rosscon/Rook/Mods/Hotend/MGN9C_HotendMount.stl

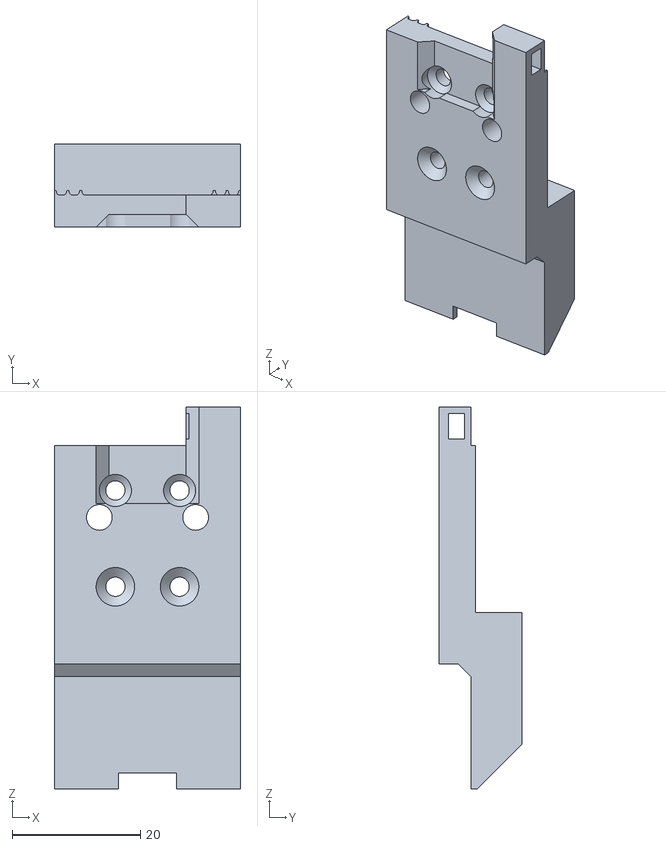
[picture p22: CAD file, 2023-01-01]
Mods/Hotend/MGN9C_HotendMount.stl
29.0 x 13.0 x 59.5
