rosscon/Rook/Mods/PrintBed/PrintBedFrame.stl

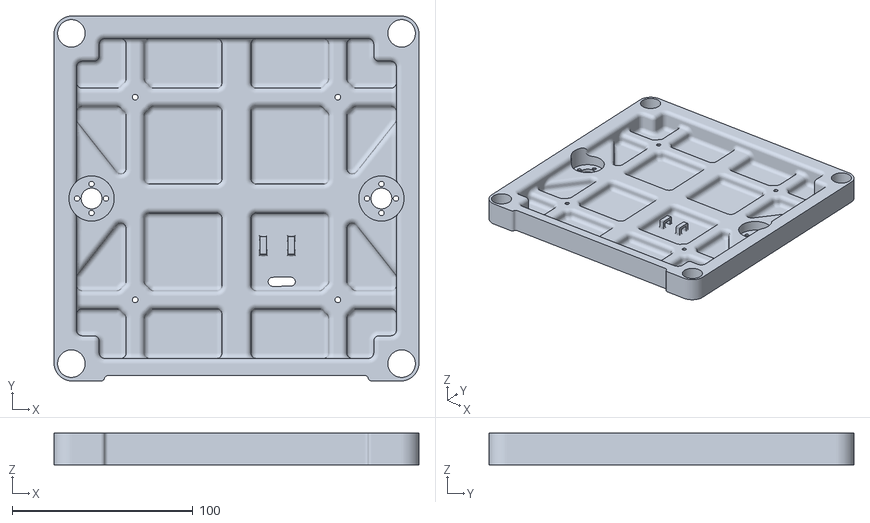
[picture p23: CAD file, 2022-11-28]
Mods/PrintBed/PrintBedFrame.stl
201.7 x 201.7 x 17.5
