rosscon/Rook/STLs/Layer Cooling/120mm blower_Mount.stl

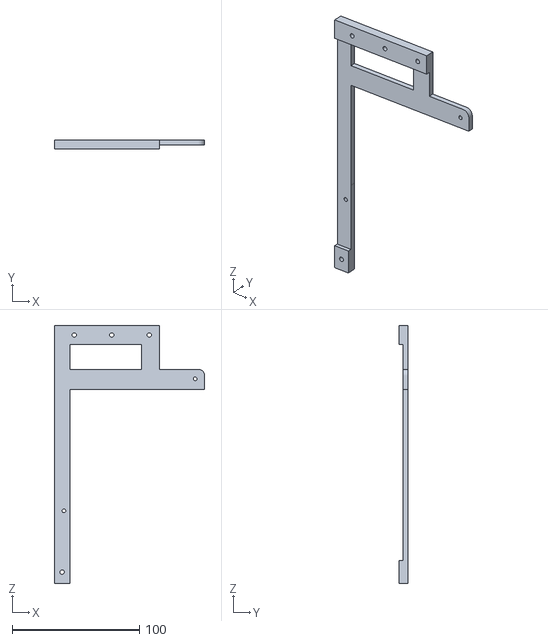
[picture p24: CAD file, 2022-12-05]
STLs/Layer Cooling/120mm blower_Mount.stl
118.4 x 7.00 x 203.0
