rosscon/Rook/STLs/X_Carriage_CR10_Style.stl

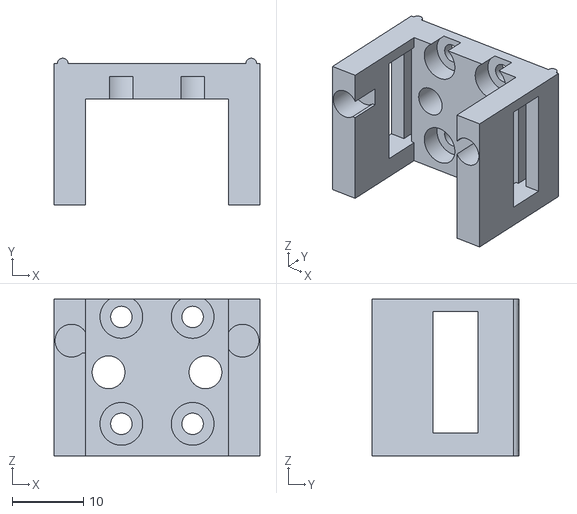
[picture p25: CAD file, 2022-12-05]
STLs/X_Carriage_CR10_Style.stl
28.9 x 20.6 x 22.0
