rosscon/Rook/User_Mods/Mods by Gulsifer/Rook_Rod_All_linear_Rod_version/CAD/V1Rook_Top Frame ROD MOD.STEP

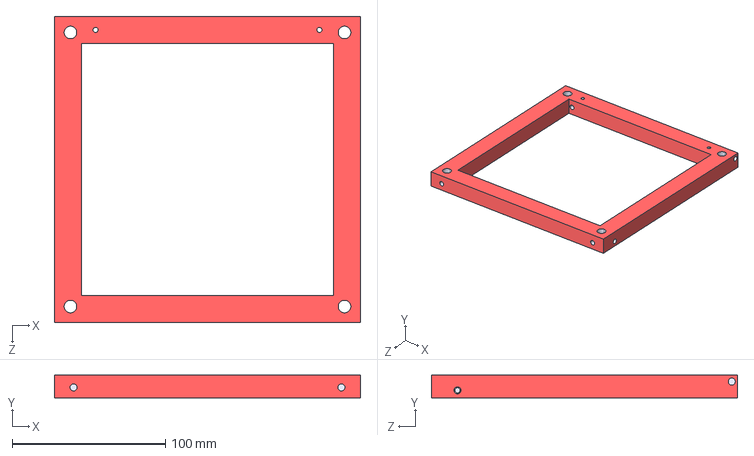
[picture p26: CAD file, 2022-12-05]
User_Mods/Mods by Gulsifer/Rook_Rod_All_linear_Rod_version/CAD/V1Rook_Top Frame ROD MOD.STEP
200.0 x 15.0 x 200.0 mm
