rosscon/Rook/User_Mods/Mods by Leviathan3DPrinting/Ender 3 v2 motor mounts/STLs/Y_MOTOR.stl

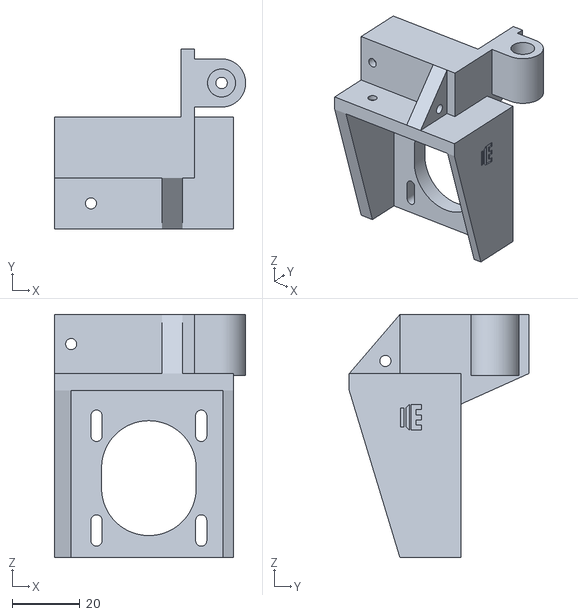
[picture p27: CAD file, 2022-12-05]
User_Mods/Mods by Leviathan3DPrinting/Ender 3 v2 motor mounts/STLs/Y_MOTOR.stl
56.7 x 53.2 x 71.9
