rosscon/Rook/Mods/Fan Bracket/FanBracket.stl

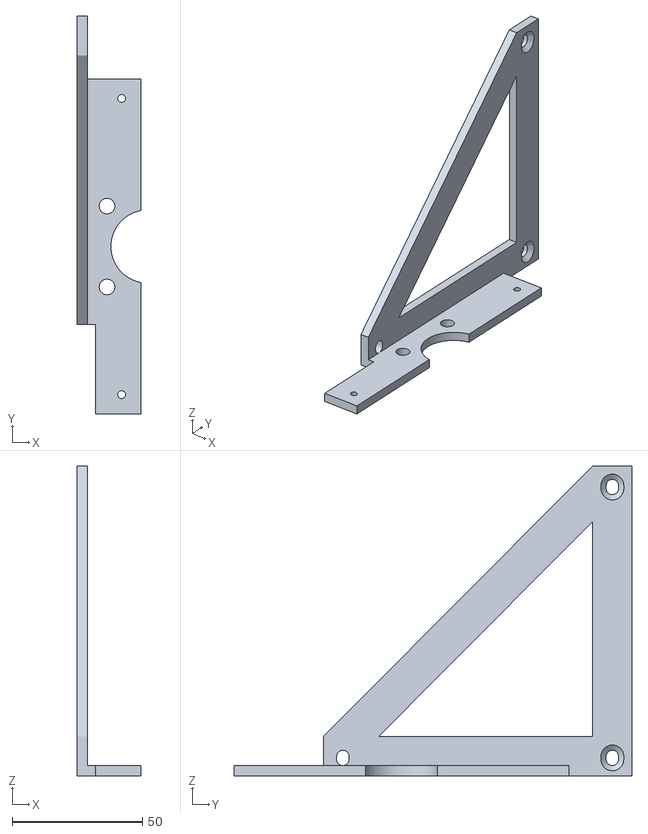
[picture p28: CAD file, 2022-11-20]
Mods/Fan Bracket/FanBracket.stl
24.5 x 152.5 x 118.8
