rosscon/Rook/Mods/Frame/exo_backbox.stl

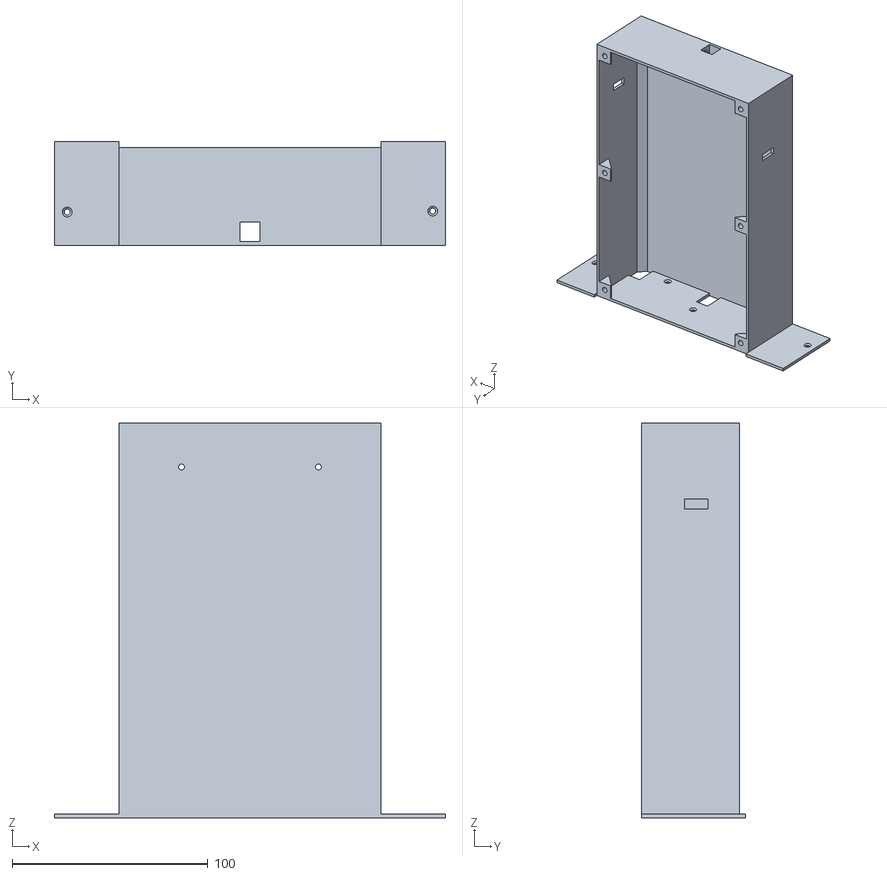
[picture p29: CAD file, 2023-01-01]
Mods/Frame/exo_backbox.stl
200.0 x 53.0 x 202.0
