rosscon/Rook/Mods/PrintBed/PrintBedTop.stl

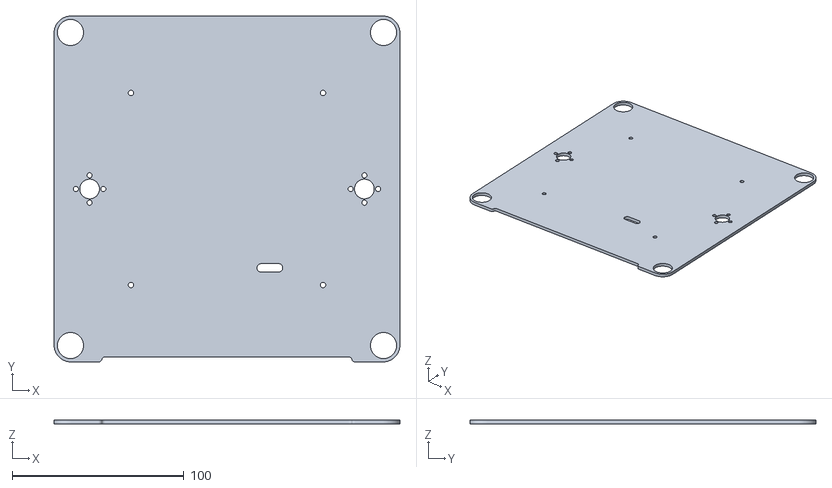
[picture p30: CAD file, 2022-11-28]
Mods/PrintBed/PrintBedTop.stl
201.7 x 201.7 x 2.50
