rosscon/Rook/STLs/Bed_Pad_for_springs.stl

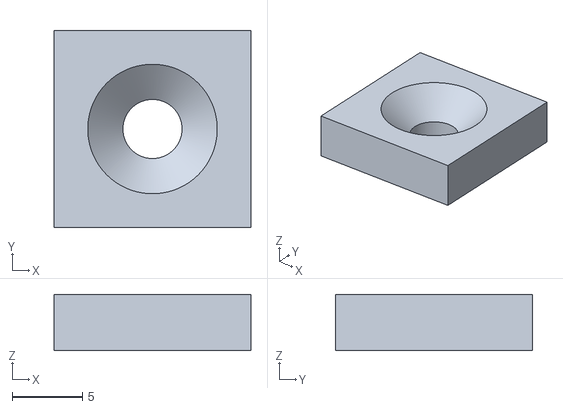
[picture p31: CAD file, 2022-12-05]
STLs/Bed_Pad_for_springs.stl
14.0 x 14.0 x 4.00
