rosscon/Rook/STLs/Frame/Top_Frame.stl

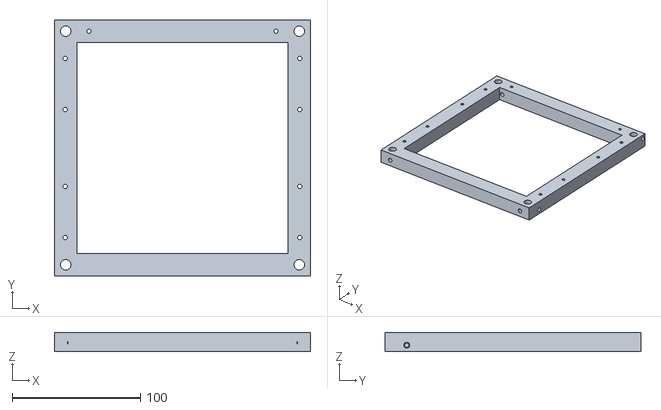
[picture p32: CAD file, 2022-12-05]
STLs/Frame/Top_Frame.stl
200.0 x 200.0 x 15.0
