rosscon/Rook/STLs/Gantry/Y_Carriage_Left_polished_MK1.stl

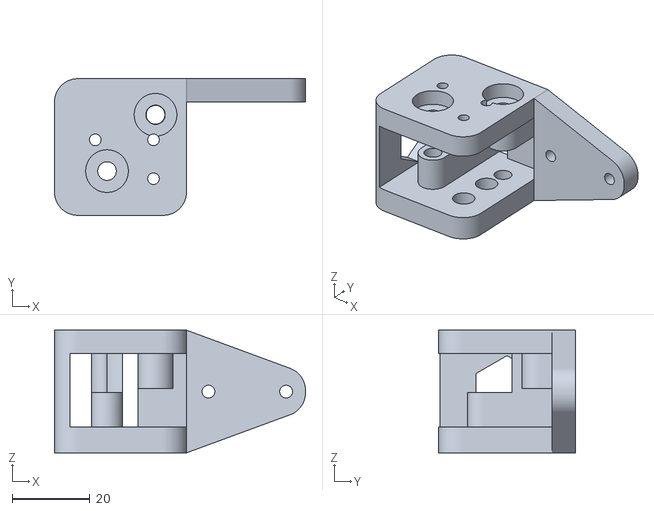
[picture p33: CAD file, 2022-12-05]
STLs/Gantry/Y_Carriage_Left_polished_MK1.stl
64.7 x 35.2 x 31.6
