rosscon/Rook/User_Mods/Mods by Gulsifer/Rook_Rod_All_linear_Rod_version/CAD/V1Y_Carriage_Right ROD MOD.STEP

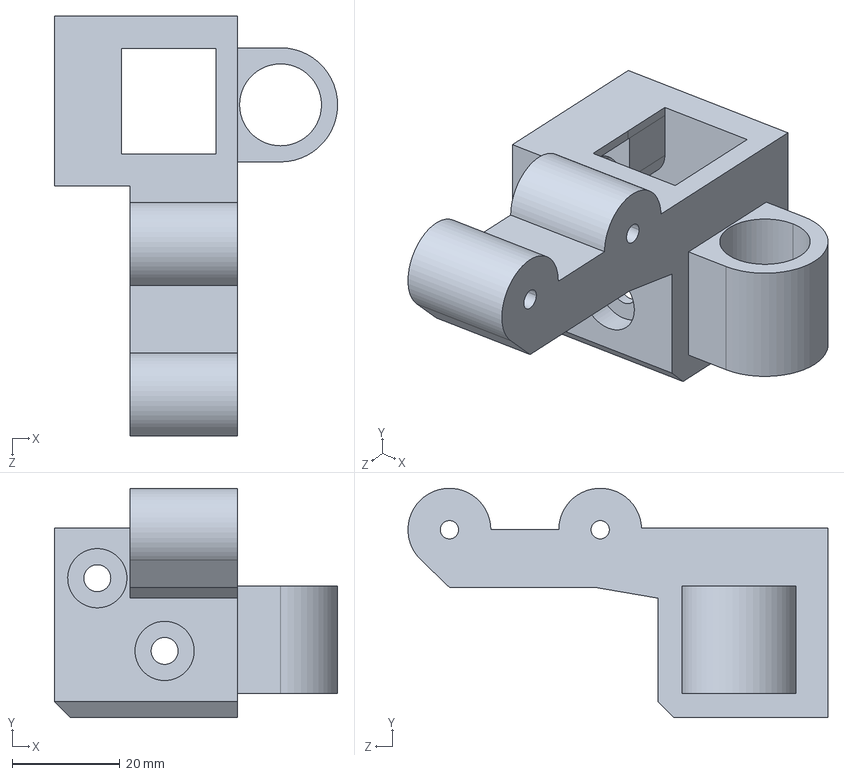
[picture p34: CAD file, 2022-12-05]
User_Mods/Mods by Gulsifer/Rook_Rod_All_linear_Rod_version/CAD/V1Y_Carriage_Right ROD MOD.STEP
52.6 x 42.6 x 78.0 mm
