rosscon/Rook/Mods/Frame/Endstop mount.stl

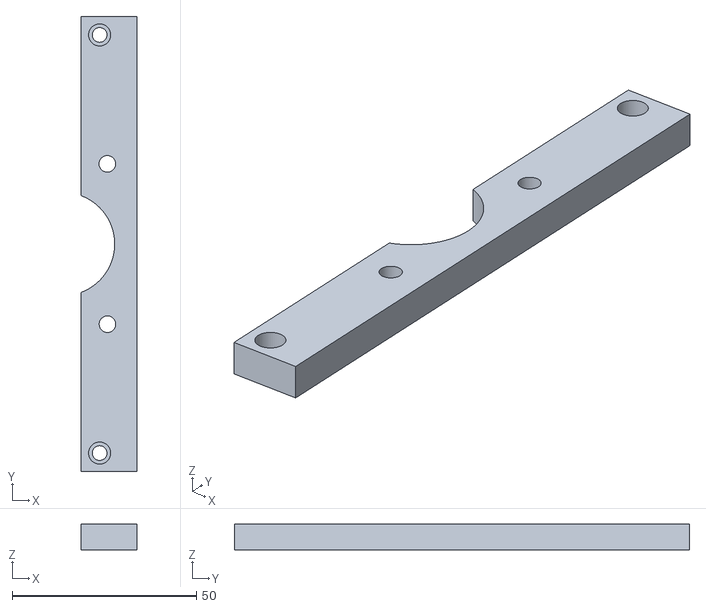
[picture p35: CAD file, 2023-01-01]
Mods/Frame/Endstop mount.stl
15.1 x 123.5 x 7.00
