rosscon/Rook/STLs/Frame/Bed_Frame.stl

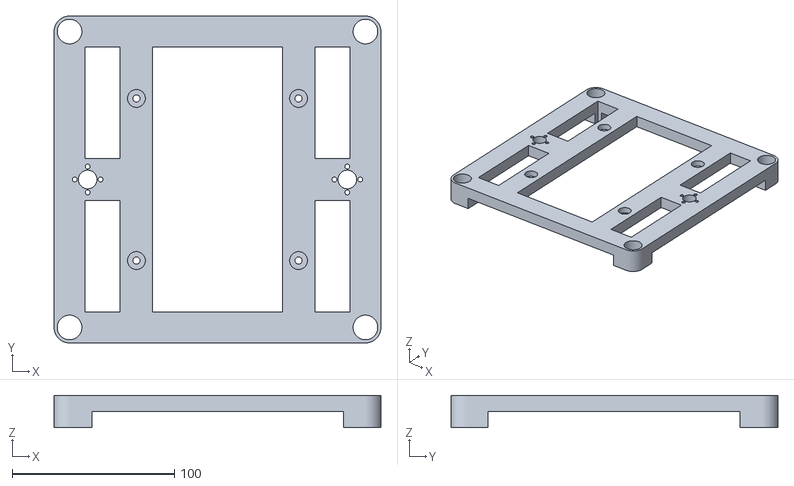
[picture p36: CAD file, 2022-12-05]
STLs/Frame/Bed_Frame.stl
201.7 x 201.7 x 20.0
