rosscon/Rook/User_Mods/Mods by Gulsifer/Rook_Rod_All_linear_Rod_version/CAD/V1Rook_Base Frame 2.1.STEP

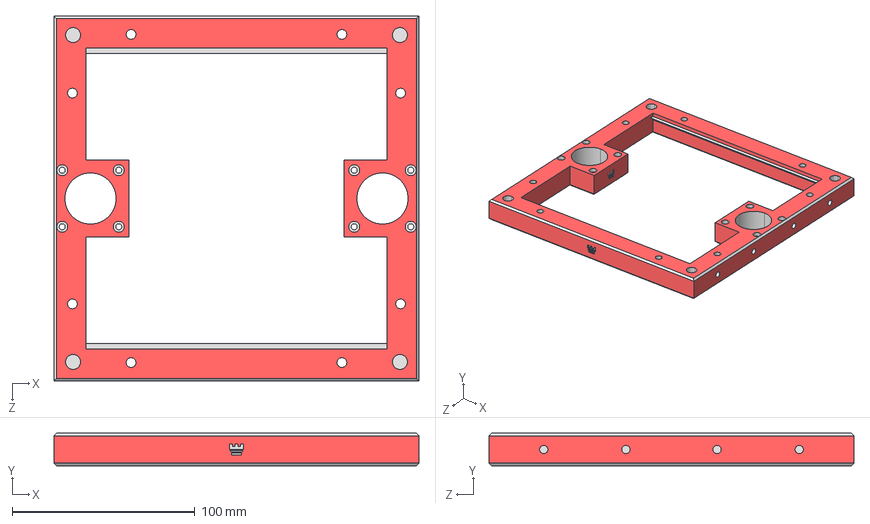
[picture p37: CAD file, 2022-12-05]
User_Mods/Mods by Gulsifer/Rook_Rod_All_linear_Rod_version/CAD/V1Rook_Base Frame 2.1.STEP
200.0 x 18.0 x 200.0 mm
