rosscon/Rook/Mods/Frame/Right_Motor_Mount.stl

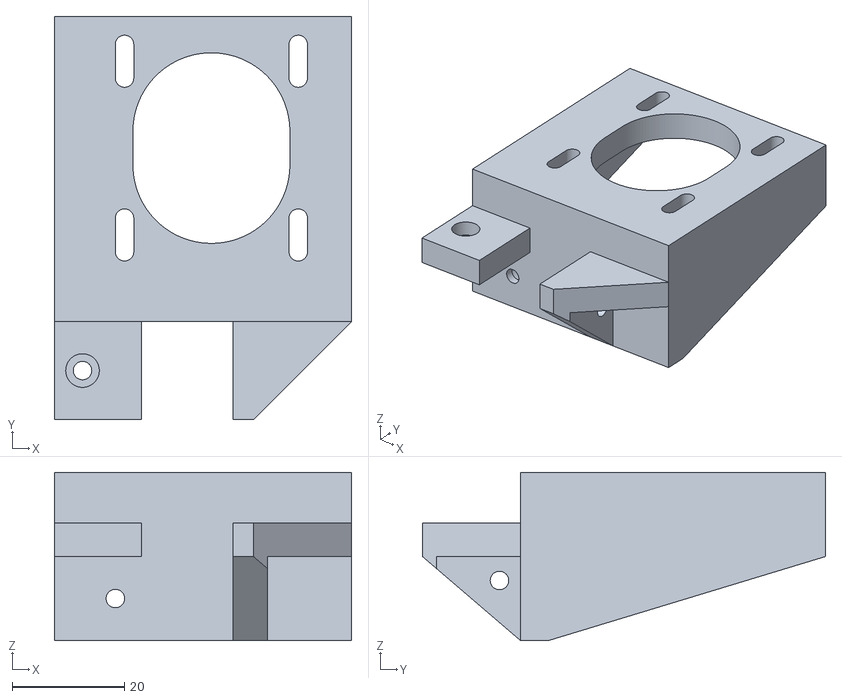
[picture p38: CAD file, 2023-01-01]
Mods/Frame/Right_Motor_Mount.stl
53.0 x 71.9 x 30.0
