rosscon/Rook/STLs/Frame/Z_endstop_Mount.stl

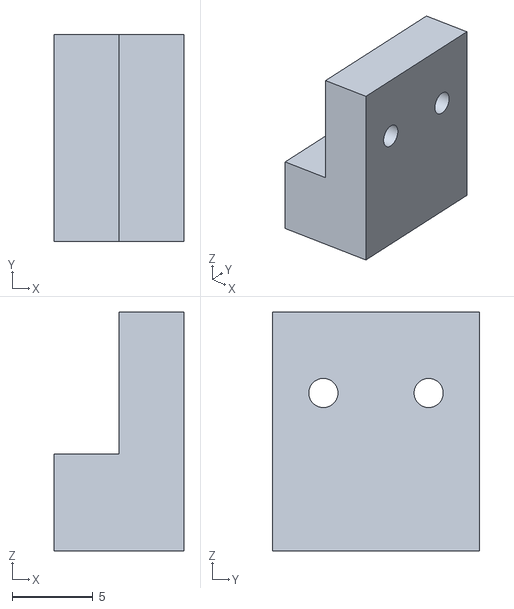
[picture p39: CAD file, 2022-12-05]
STLs/Frame/Z_endstop_Mount.stl
8.00 x 12.8 x 14.8
