rosscon/Rook/Mods/Frame/exo_backboxlid.stl

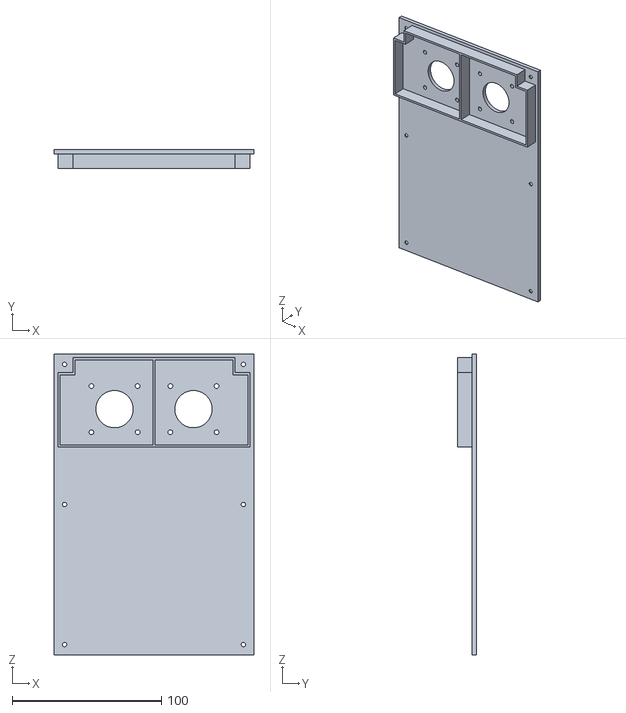
[picture p40: CAD file, 2023-01-01]
Mods/Frame/exo_backboxlid.stl
134.0 x 13.0 x 202.0
