rosscon/Rook/User_Mods/Mods by Gulsifer/Rook_Rod_All_linear_Rod_version/CAD/V1Right_Idler ROD MOD.STEP

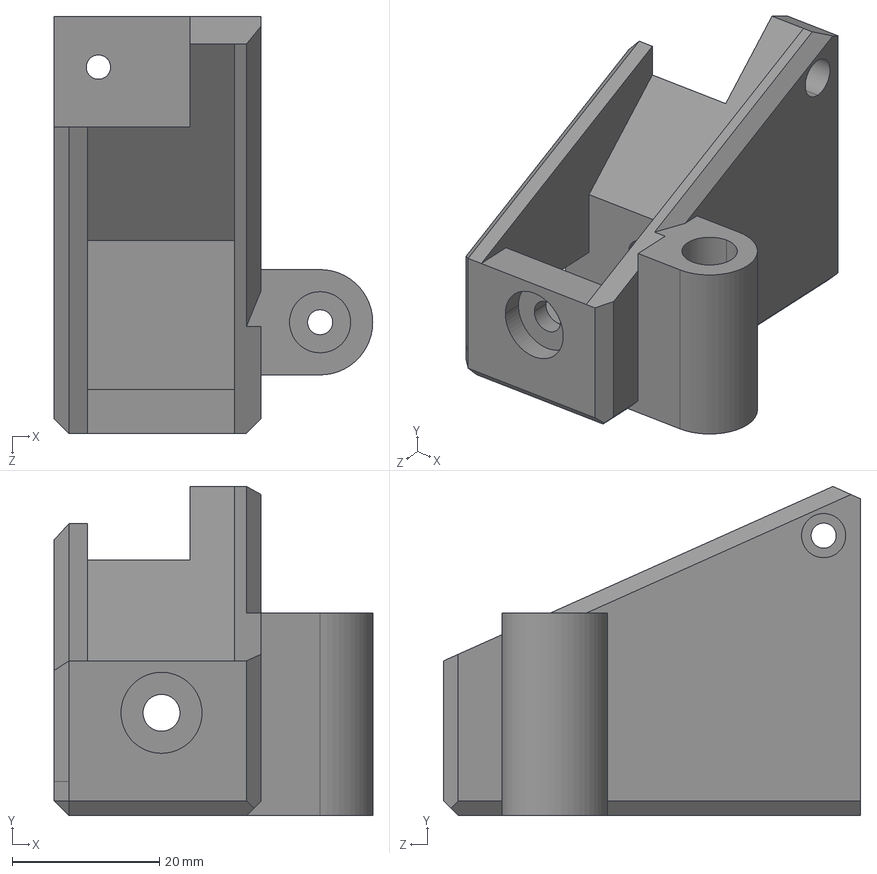
[picture p41: CAD file, 2022-12-05]
User_Mods/Mods by Gulsifer/Rook_Rod_All_linear_Rod_version/CAD/V1Right_Idler ROD MOD.STEP
43.2 x 44.7 x 56.6 mm
