rosscon/Rook/Mods/Frame/backbase.stl

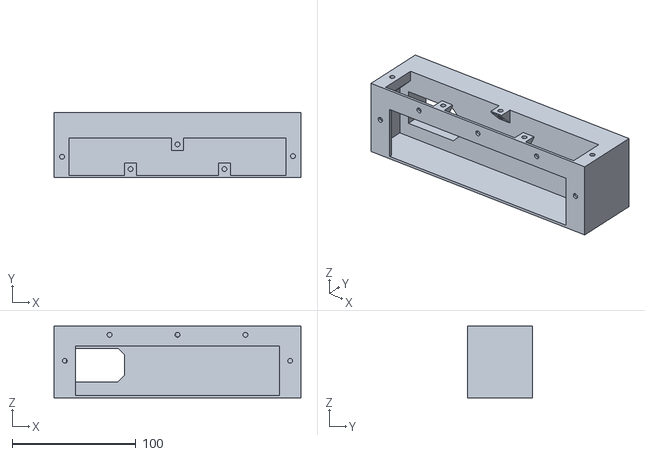
[picture p42: CAD file, 2023-01-01]
Mods/Frame/backbase.stl
200.0 x 53.0 x 58.0
