rosscon/Rook/User_Mods/Mods by Gulsifer/Rook_Rod_All_linear_Rod_version/CAD/V1Rook_Top Left Motor Mount ROD MOD.STEP

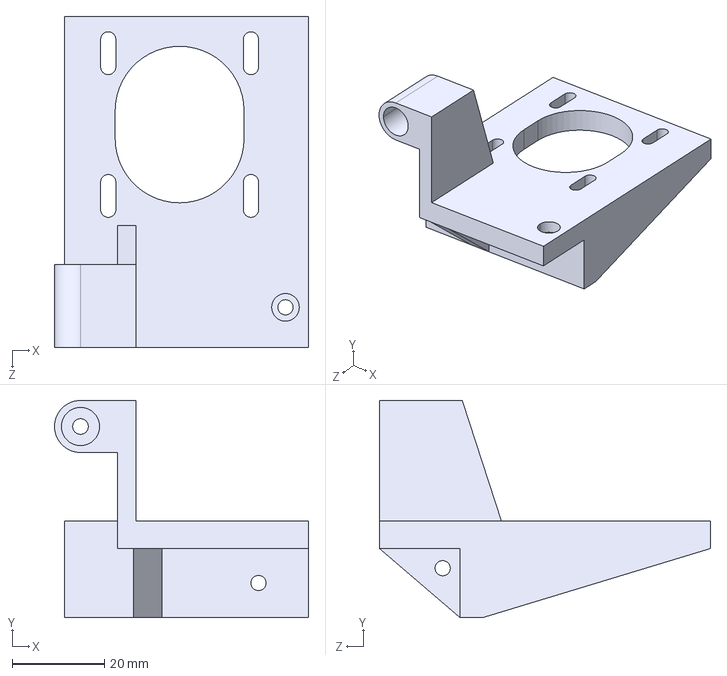
[picture p43: CAD file, 2022-12-05]
User_Mods/Mods by Gulsifer/Rook_Rod_All_linear_Rod_version/CAD/V1Rook_Top Left Motor Mount ROD MOD.STEP
55.2 x 47.2 x 72.0 mm
