rosscon/Rook/Mods/Frame/backbox_fan.stl

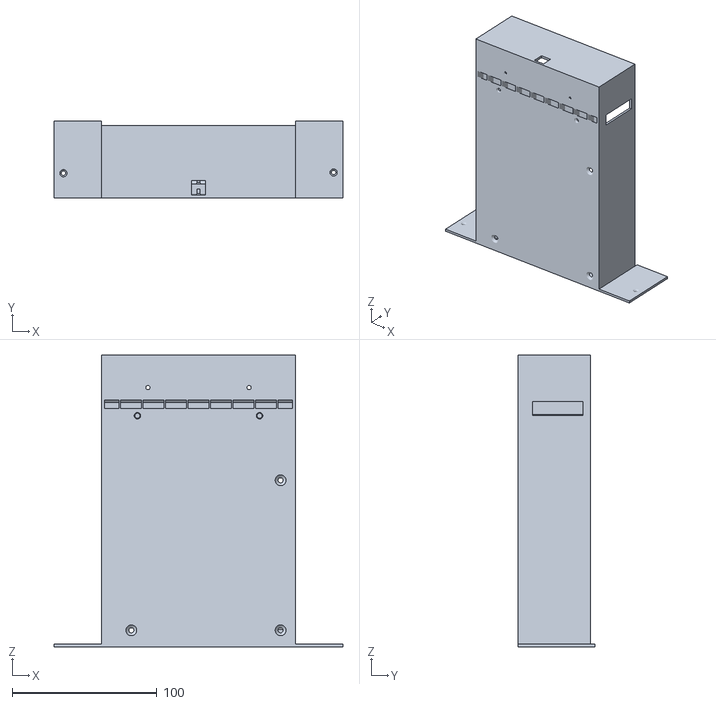
[picture p44: CAD file, 2023-01-01]
Mods/Frame/backbox_fan.stl
200.0 x 53.0 x 202.0
