rosscon/Rook/STLs/Frame/Left_Motor_Mount.stl

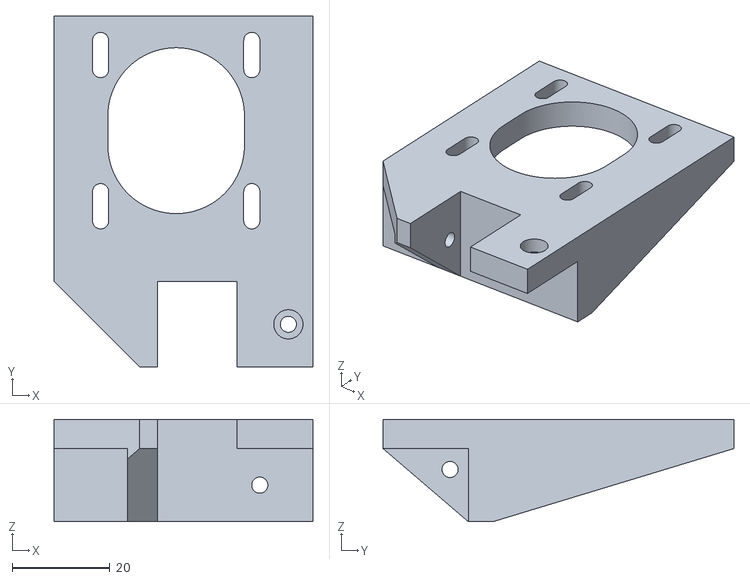
[picture p45: CAD file, 2022-12-05]
STLs/Frame/Left_Motor_Mount.stl
53.0 x 71.9 x 21.0
