rosscon/Rook/Mods/Frame/Bottom_Frame.stl

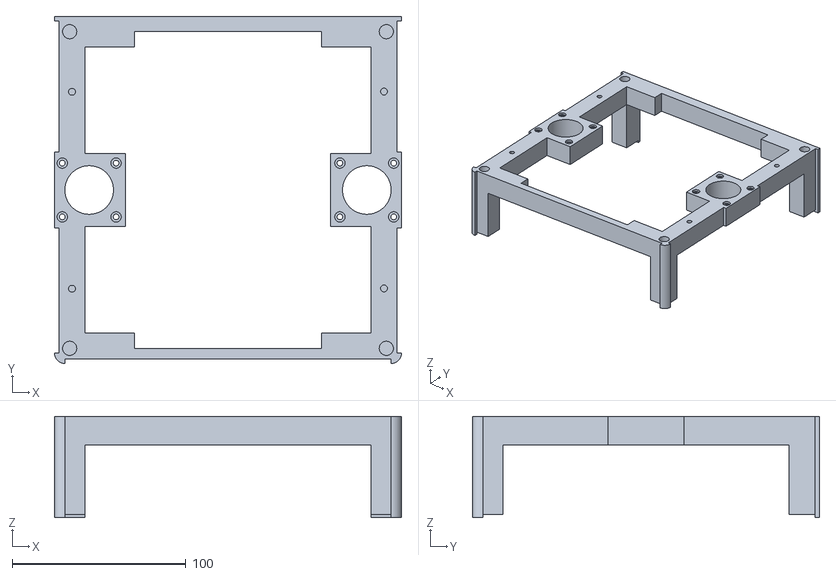
[picture p46: CAD file, 2022-12-12]
Mods/Frame/Bottom_Frame.stl
200.0 x 200.0 x 58.5
