rosscon/Rook/STLs/Frame/Bottom_Frame_MK1.stl

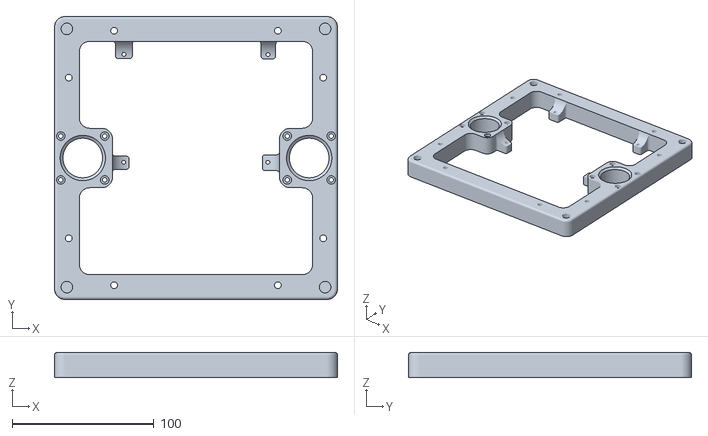
[picture p47: CAD file, 2022-12-05]
STLs/Frame/Bottom_Frame_MK1.stl
200.0 x 200.0 x 18.0
