rosscon/Rook/User_Mods/Mods by Gulsifer/Rook_Rod_All_linear_Rod_version/CAD/V1Left_Idler ROD MOD.STEP

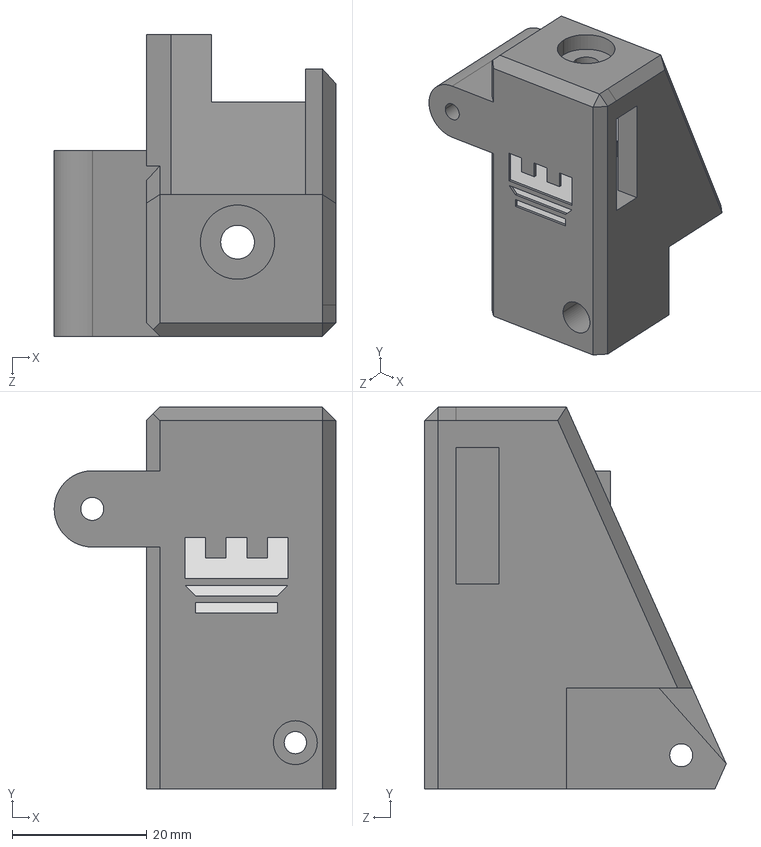
[picture p48: CAD file, 2022-12-05]
User_Mods/Mods by Gulsifer/Rook_Rod_All_linear_Rod_version/CAD/V1Left_Idler ROD MOD.STEP
41.7 x 56.6 x 44.7 mm
