rosscon/Rook/Mods/Frame/PSU_Safety Cover.stl

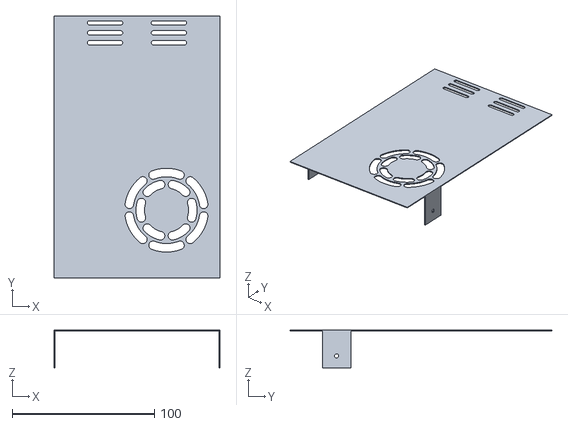
[picture p49: CAD file, 2022-12-12]
Mods/Frame/PSU_Safety Cover.stl
116.9 x 184.5 x 26.6
