rosscon/Rook/STLs/Frame/Right_Motor_Mount.stl

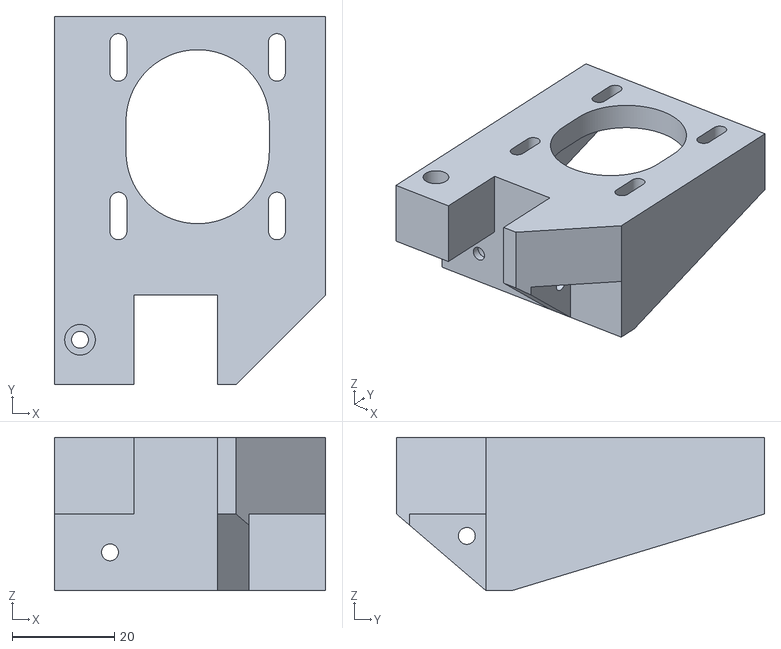
[picture p50: CAD file, 2022-12-05]
STLs/Frame/Right_Motor_Mount.stl
53.0 x 71.9 x 30.0
