rosscon/Rook/User_Mods/Mods by Gulsifer/Rook_Rod_All_linear_Rod_version/CAD/V1Rook_Top Right Motor Mount ROD MOD.STEP

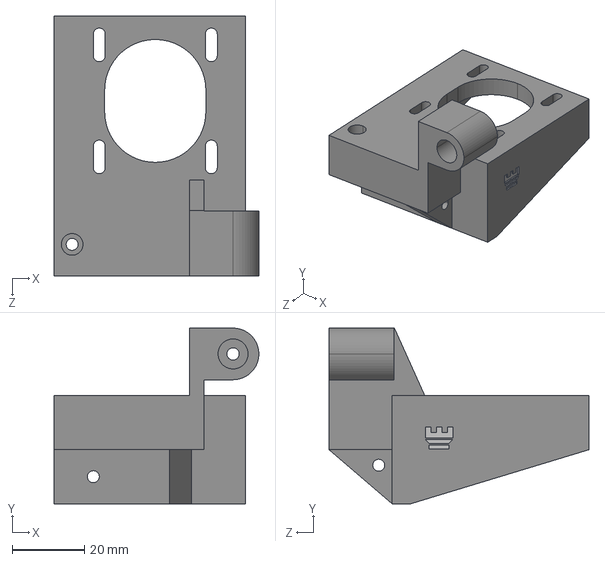
[picture p51: CAD file, 2022-12-05]
User_Mods/Mods by Gulsifer/Rook_Rod_All_linear_Rod_version/CAD/V1Rook_Top Right Motor Mount ROD MOD.STEP
56.7 x 48.6 x 72.0 mm
