rosscon/Rook/Mods/Frame/Bottom_Frame_topper.stl

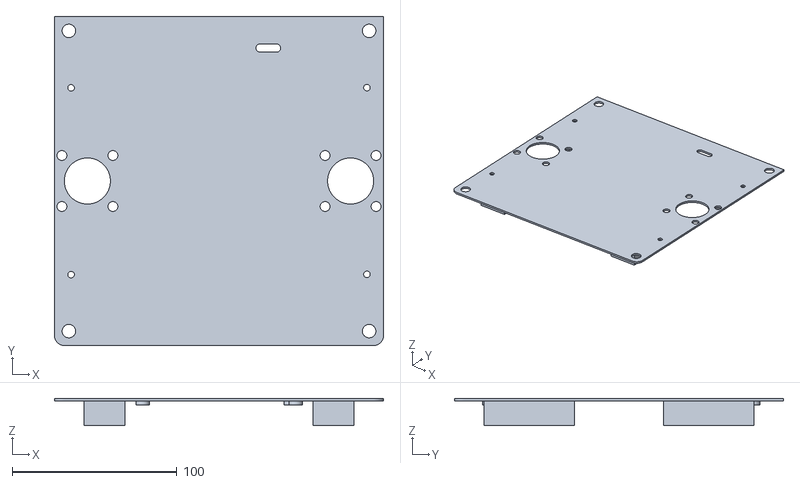
[picture p52: CAD file, 2022-12-12]
Mods/Frame/Bottom_Frame_topper.stl
200.0 x 200.0 x 16.5
