rosscon/Rook/User_Mods/Mods by Gulsifer/Rook_Rod_All_linear_Rod_version/CAD/V1Rook_Foot Mount_3.0.STEP

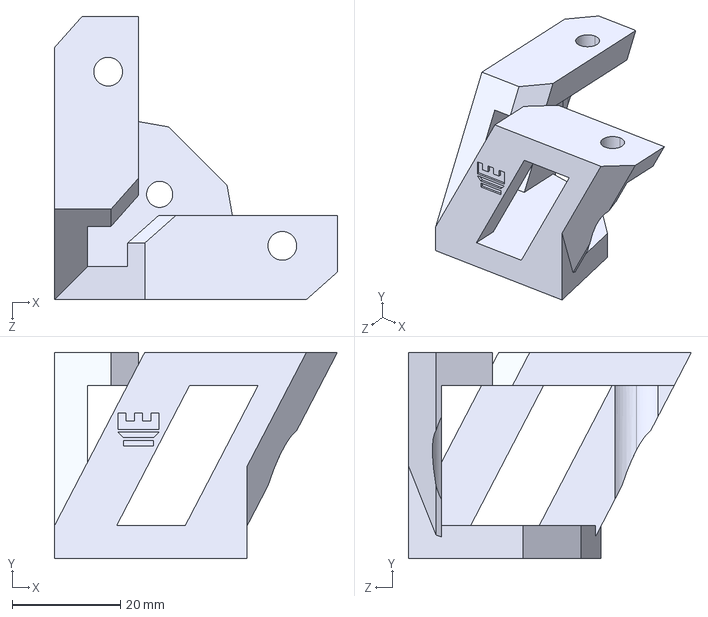
[picture p53: CAD file, 2022-12-05]
User_Mods/Mods by Gulsifer/Rook_Rod_All_linear_Rod_version/CAD/V1Rook_Foot Mount_3.0.STEP
52.2 x 38.1 x 52.2 mm
