rosscon/Rook/Mods/Frame/Fan Grill 40mm.stl

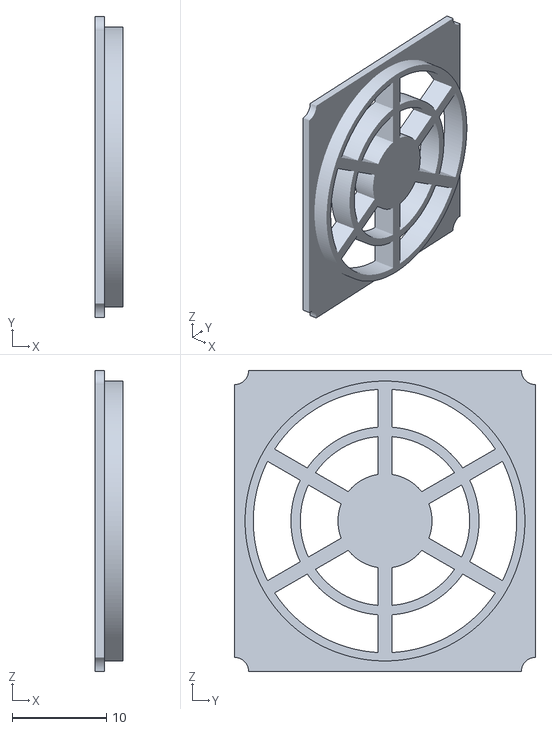
[picture p54: CAD file, 2022-12-05]
Mods/Frame/Fan Grill 40mm.stl
3.00 x 32.0 x 32.0
