rosscon/Rook/Mods/Frame/vent.stl

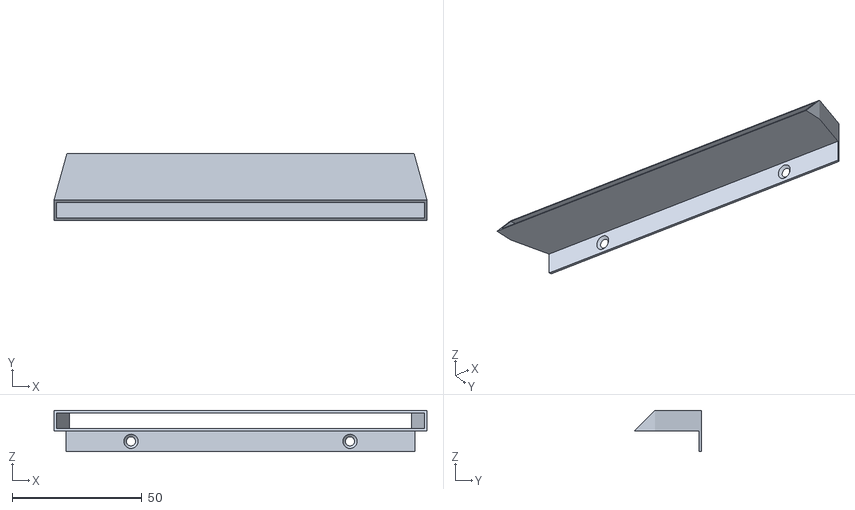
[picture p55: CAD file, 2022-12-05]
Mods/Frame/vent.stl
144.0 x 26.0 x 16.0
