rosscon/Rook/Mods/Frame/Bottom_Frame_pnl_fan_fl.stl

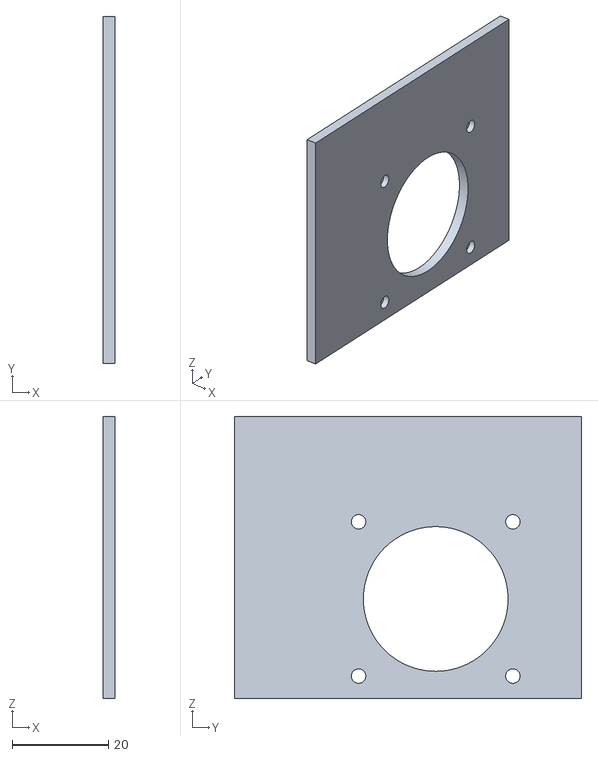
[picture p56: CAD file, 2022-11-28]
Mods/Frame/Bottom_Frame_pnl_fan_fl.stl
2.50 x 72.0 x 58.5
