rosscon/Rook/Mods/Frame/Bottom_Frame_pnl_fan_rr.stl

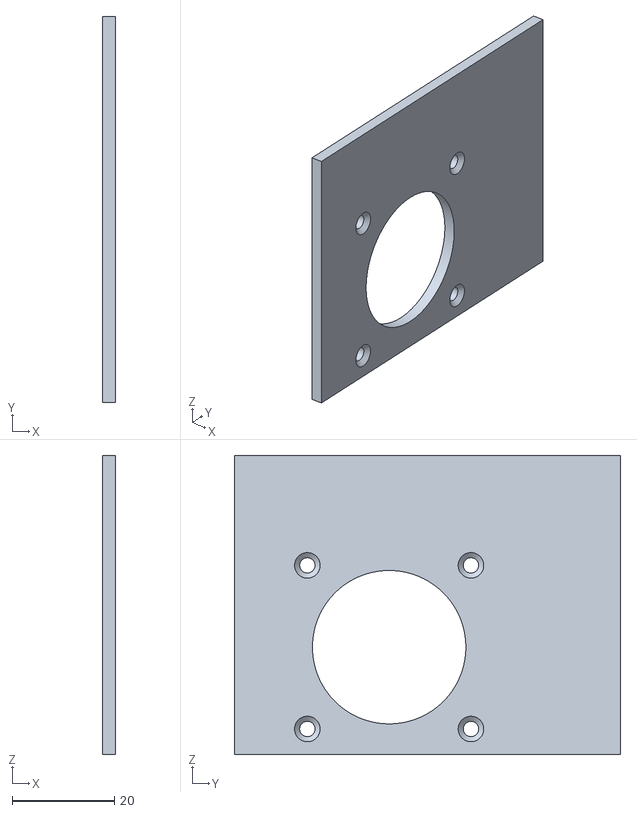
[picture p57: CAD file, 2022-11-28]
Mods/Frame/Bottom_Frame_pnl_fan_rr.stl
2.50 x 75.5 x 58.5
