rosscon/Rook/Mods/Frame/Bottom_Frame_pnl_front.stl

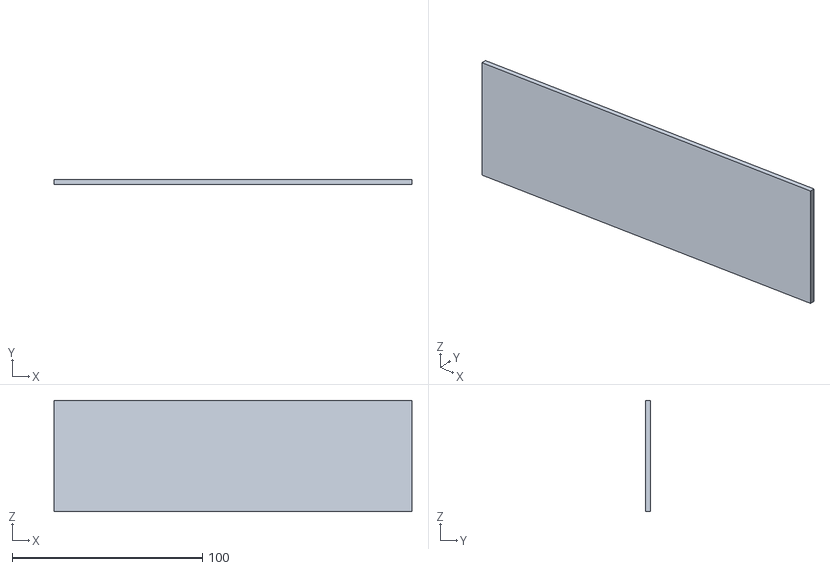
[picture p58: CAD file, 2022-11-28]
Mods/Frame/Bottom_Frame_pnl_front.stl
188.0 x 2.50 x 58.5
