rosscon/Rook/Mods/Frame/Top_Frame.stl

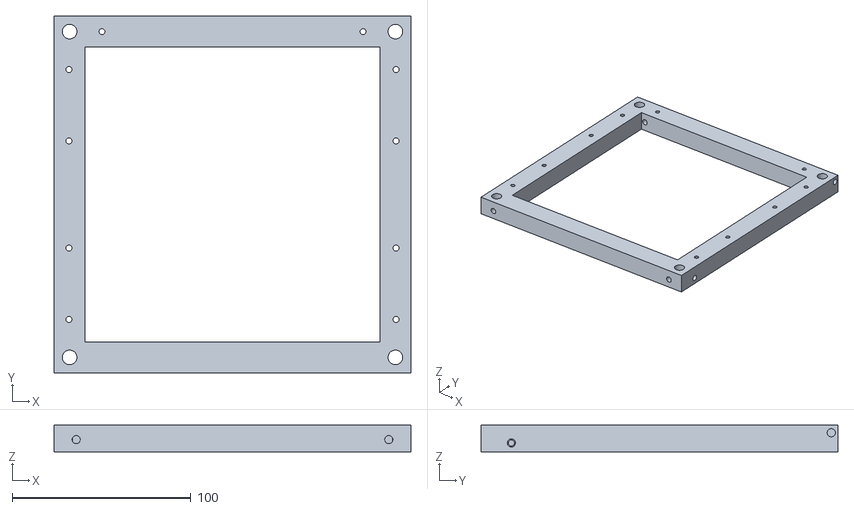
[picture p59: CAD file, 2022-11-20]
Mods/Frame/Top_Frame.stl
200.0 x 200.0 x 15.0
